OpenWise/wiseup/src/linux/include/pcd8544.h

/*
 * Author: Yevgeniy Kiveisha <yevgeniy.kiveisha@intel.com>
 * Copyright (c) 2014 Intel Corporation.
 */
 
#pragma once

#include <string>
#include <gpio.h>
#include <spi.h>
#include <stdio.h>
#include <cstring>

#include "gfx.h"

#define BLACK 1
#define WHITE 0

#define LCDWIDTH 84
#define LCDHEIGHT 48

#define PCD8544_POWERDOWN 			0x04
#define PCD8544_ENTRYMODE 			0x02
#define PCD8544_EXTENDEDINSTRUCTION 0x01

#define PCD8544_DISPLAYBLANK 		0x0
#define PCD8544_DISPLAYNORMAL 		0x4
#define PCD8544_DISPLAYALLON 		0x1
#define PCD8544_DISPLAYINVERTED 	    0x5

// H = 0
#define PCD8544_FUNCTIONSET 		    0x20
#define PCD8544_DISPLAYCONTROL 		0x08
#define PCD8544_SETYADDR 			0x40
#define PCD8544_SETXADDR 			0x80

// H = 1
#define PCD8544_SETTEMP 			    0x04
#define PCD8544_SETBIAS 			    0x10
#define PCD8544_SETVOP 				0x80

#define HIGH            			1
#define LOW             			0

static const unsigned char font[] = {
    0x00, 0x00, 0x00, 0x00, 0x00,
	0x3E, 0x5B, 0x4F, 0x5B, 0x3E,
	0x3E, 0x6B, 0x4F, 0x6B, 0x3E,
	0x1C, 0x3E, 0x7C, 0x3E, 0x1C,
	0x18, 0x3C, 0x7E, 0x3C, 0x18,
	0x1C, 0x57, 0x7D, 0x57, 0x1C,
	0x1C, 0x5E, 0x7F, 0x5E, 0x1C,
	0x00, 0x18, 0x3C, 0x18, 0x00,
	0xFF, 0xE7, 0xC3, 0xE7, 0xFF,
	0x00, 0x18, 0x24, 0x18, 0x00,
	0xFF, 0xE7, 0xDB, 0xE7, 0xFF,
	0x30, 0x48, 0x3A, 0x06, 0x0E,
	0x26, 0x29, 0x79, 0x29, 0x26,
	0x40, 0x7F, 0x05, 0x05, 0x07,
	0x40, 0x7F, 0x05, 0x25, 0x3F,
	0x5A, 0x3C, 0xE7, 0x3C, 0x5A,
	0x7F, 0x3E, 0x1C, 0x1C, 0x08,
	0x08, 0x1C, 0x1C, 0x3E, 0x7F,
	0x14, 0x22, 0x7F, 0x22, 0x14,
	0x5F, 0x5F, 0x00, 0x5F, 0x5F,
	0x06, 0x09, 0x7F, 0x01, 0x7F,
	0x00, 0x66, 0x89, 0x95, 0x6A,
	0x60, 0x60, 0x60, 0x60, 0x60,
	0x94, 0xA2, 0xFF, 0xA2, 0x94,
	0x08, 0x04, 0x7E, 0x04, 0x08,
	0x10, 0x20, 0x7E, 0x20, 0x10,
	0x08, 0x08, 0x2A, 0x1C, 0x08,
	0x08, 0x1C, 0x2A, 0x08, 0x08,
	0x1E, 0x10, 0x10, 0x10, 0x10,
	0x0C, 0x1E, 0x0C, 0x1E, 0x0C,
	0x30, 0x38, 0x3E, 0x38, 0x30,
	0x06, 0x0E, 0x3E, 0x0E, 0x06,
	0x00, 0x00, 0x00, 0x00, 0x00,
	0x00, 0x00, 0x5F, 0x00, 0x00,
	0x00, 0x07, 0x00, 0x07, 0x00,
	0x14, 0x7F, 0x14, 0x7F, 0x14,
	0x24, 0x2A, 0x7F, 0x2A, 0x12,
	0x23, 0x13, 0x08, 0x64, 0x62,
	0x36, 0x49, 0x56, 0x20, 0x50,
	0x00, 0x08, 0x07, 0x03, 0x00,
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
};

class PCD8544 : public GFX {
public:
	PCD8544 (spi_context& spi, uint8_t cs, uint8_t dc, uint8_t rst);
	PCD8544 (uint8_t cs, uint8_t dc, uint8_t rst);
	~PCD8544 ();
	
	void init ();
	void setContrast (uint8_t contrast);
	void drawPixel(int16_t x, int16_t y, uint16_t color);
	void setAddrWindow (uint8_t x0, uint8_t y0, uint8_t x1, uint8_t y1);
	void refresh ();
	void clearscr ();
	void drawFromBuffer (uint8_t * rawData);

	void powerUp ();
	void powerDown ();
	
private:
	void cmd (uint8_t data);
	void data (uint8_t data);
	
	spi_context     m_spi;
	gpio_context    m_csCtx;
	gpio_context    m_dcCtx; // Data Controll
	gpio_context    m_rstCtx;
	
	uint8_t			m_contrast;
	uint8_t			m_bias;
	uint8_t			m_rotation;
};
