OpenWise/wiseup/src/linux/include/wiseApplication.h

/*
 * Author: Yevgeniy Kiveisha <lodmilak@gmail.com>
 * Copyright (c) 2014 OpenWise.
 */

#pragma once

#include <iostream>
#include <pthread.h>
#include <vector>
#include <stdlib.h>

#include "wise_rfcomm.hpp"
#include "wise_ipc.h"
#include "commonMethods.hpp"
#include "wise_mysql.h"

#define MAX_EXECUTORS	20

using namespace std;

typedef struct {
	uint64_t 	appId;
	std::string appName;
	std::string	appDescription;
	std::string	appInstallDate;
	bool		isAvailable;
	std::string	appDatabase;
	vector<uint64_t> attachedSensorIDList;
} app_info_t;

class ApllicationExecutor {
public:
	ApllicationExecutor ();
	~ApllicationExecutor ();
	
	void execute (char * path);
	
	char scripPath[256];
	bool isAvailable;

private:
	pthread_t m_worker;
};

class WiseApplicationManager {
public:
	WiseApplicationManager ();
	~WiseApplicationManager ();
	
	bool getAllApplications ();
	app_info_t * findApplication (uint64_t appID);
	
	ApllicationExecutor* getFreeExecutor ();
	
	void printApplicationsInfo ();
	
	sync_context_t	app_lock;
	sync_context_t	exec_lock;
	
private:
	vector<app_info_t>	m_applications;
	ApllicationExecutor m_executors[MAX_EXECUTORS];
	MySQL *				m_dbconn;
};
