OpenWise/wiseup/src/linux/test/client-unix-domain.c

#include <sys/socket.h>
#include <sys/un.h>
#include <stdio.h>
#include <stdlib.h>
#include <unistd.h>

//char *socket_path = "./socket";
char *socket_path = "\0hidden";

int main(int argc, char *argv[]) {
    struct sockaddr_un addr;
    char buf[5] = {'1','2','3','4','5'};
    int fd,rc;

    if (argc > 1) socket_path=argv[1];

    if ( (fd = socket(AF_UNIX, SOCK_STREAM, 0)) == -1) {
        perror("socket error");
        exit(-1);
    }

    memset(&addr, 0, sizeof(addr));
    addr.sun_family = AF_UNIX;
    strncpy(addr.sun_path, socket_path, sizeof(addr.sun_path)-1);

    if (connect(fd, (struct sockaddr*)&addr, sizeof(addr)) == -1) {
        perror("connect error");
        exit(-1);
    }

    //strcpy(buf, "hello");

    // while( (rc=read(STDIN_FILENO, buf, sizeof(buf))) > 0) {
        if (write(fd, buf, sizeof(buf)) != rc) {
            printf ("rc = %d\n", rc);
            if (rc > 0) fprintf(stderr,"partial write");
            else {
                perror("write error");
                exit(-1);
                }
        }
    // }

    return 0;
}
